scottlbaker/tzxduino-mini/firmware/display.h

//=========================================================================
//
//  display.h  -- OLED font and logo bitmaps
//
//=========================================================================

// 'Arduitape_128x32'
const byte tzx_logo[] PROGMEM = {
  0x00, 0x00, 0x00, 0x00, 0x00, 0x00, 0x00, 0x00, 0x00, 0x00, 0x00, 0x00, 0x00, 0x00, 0x00, 0x00,
  0x00, 0x00, 0x00, 0x00, 0x00, 0x00, 0x00, 0x00, 0x00, 0x00, 0x00, 0x00, 0x00, 0x00, 0x00, 0x00,
  0x00, 0x00, 0x00, 0x00, 0x00, 0x00, 0x00, 0x00, 0x00, 0x00, 0x00, 0x00, 0x00, 0x00, 0x00, 0x00,
  0x00, 0x00, 0x00, 0x00, 0x00, 0x00, 0x00, 0x00, 0x00, 0x00, 0x00, 0x00, 0x00, 0x00, 0x00, 0x00,
  0x00, 0x00, 0x00, 0x00, 0x00, 0x00, 0x00, 0x00, 0x00, 0x00, 0x00, 0x00, 0x00, 0x80, 0x80, 0x80,
  0x80, 0x80, 0x80, 0x80, 0x80, 0x80, 0x80, 0x80, 0x80, 0x80, 0x80, 0x80, 0x80, 0x80, 0x80, 0x80,
  0x80, 0x80, 0x80, 0x80, 0x80, 0x80, 0x80, 0x80, 0x80, 0x80, 0x80, 0x80, 0x80, 0x80, 0x80, 0x80,
  0x80, 0x80, 0x80, 0x80, 0x80, 0x80, 0x80, 0x80, 0x80, 0x80, 0x80, 0x80, 0x80, 0x00, 0x00, 0x00,
  0x00, 0x00, 0x00, 0x00, 0x00, 0x00, 0x00, 0x00, 0x00, 0x80, 0xe0, 0xf0, 0xf8, 0xf8, 0xf8, 0xf8,
  0xf8, 0xf0, 0x80, 0x00, 0x00, 0x00, 0x80, 0xe0, 0xf8, 0xf8, 0xf8, 0xf8, 0xf0, 0xe0, 0x80, 0x00,
  0x00, 0x00, 0x00, 0x00, 0x00, 0x00, 0x80, 0xb8, 0xb8, 0xb8, 0x98, 0x00, 0x00, 0x00, 0x00, 0x00,
  0xc0, 0xc0, 0xc0, 0xc0, 0x80, 0x80, 0x80, 0x80, 0x80, 0x80, 0x80, 0x00, 0x00, 0x00, 0x00, 0x00,
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
  0x00, 0x7E, 0x42, 0x42, 0x42, 0x24, 0x18, 0x00,   // D
  0x00, 0x7E, 0x4A, 0x4A, 0x4A, 0x4A, 0x42, 0x00,   // E
  0x00, 0x7E, 0x0A, 0x0A, 0x0A, 0x0A, 0x02, 0x00,   // F
  0x00, 0x3C, 0x42, 0x42, 0x52, 0x52, 0x34, 0x00,   // G
  0x00, 0x7E, 0x08, 0x08, 0x08, 0x08, 0x7E, 0x00,   // H
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
};
